m5evt/Firecrest/firmware/display.c

/* 
 * Copyright 2021 m5evt
 * 
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
 */
 
#include <stdlib.h>

#include "firecrest.h"
#include "ssd1306.h"
#include "display.h"



static void drawNumberBig(int bigNum, int offset);
static void drawNumberSmall(int smallNum, int offset, int offsetRow);
static void drawDot(int offset);
static void drawVSWRtoOne(void);

//ICON 45x16
// Per http://www.nongnu.org/avr-libc/user-manual/pgmspace.html
const uint8_t stateIcons[NUMSTATES][ICONWIDTHbits*ICONROWSbytes] PROGMEM = { 
{0x0 , 0x0 , 0x0 , 0x0 , 0x0 , 0x0 , 0x0 , 0x0 , 0x00 , 0x00 , 0x00 , 0x00 , 0x00 , 0x0 , 0x0 , 0x0 , 0x0 , 0x0 , 0x0 , 0x0 , 0x0, 0x0, 0x0 , 0x0 , 0x0, 0x0, 0x0, 0x0, 0x0 , 0x0 , 0x0 , 0x0 , 0x0 , 0x0 , 0x0 , 0x0 , 0x0 , 0x0 , 0x0 , 0x0 , 0x0 , 0x0 , 0x0 , 0x0 , 0x0 , 0x0 , 0x0 , 0x0 , 0x0 , 0x0 , 0x0 , 0x0 , 0x0 , 0x0 , 0x0 , 0x0 , 0x0 , 0x0 , 0x0 , 0x0 , 0x0 , 0x0 , 0x0 , 0x0 , 0x0 , 0x0 , 0x0 , 0x0 , 0x0 , 0x0 , 0x0 , 0x0 , 0x0 , 0x0 , 0x0 , 0x0 , 0x0 , 0x0 , 0x0 , 0x0 , 0x0 , 0x0 , 0x0 , 0x0 , 0x0 , 0x0 , 0x0 , 0x0}, //Freq
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
};

const uint8_t vswrToOne[vswrWIDTHbits * vswrBytes] PROGMEM = {0x0 , 0x0 , 0x0 , 0x0 , 0x0 , 0x0 , 0x0 , 0x3 , 0x3 , 0xff , 0xff , 0x0 , 0x0 , 0x0 , 0x0 , 0x0 , 
0x0 , 0x70 , 0x70 , 0x70 , 0x0 , 0x0 , 0x0 , 0x0 , 0x0 , 0xff , 0xff , 0x0 , 0x0 , 0x0 , 0x0 , 0x0 , 0x0 , 0xe0 , 0xe0 , 0xe0 , 0x0 , 0x0 , 0x0 , 0xc0 , 0xc0 , 0xff , 0xff , 0xc0 , 0xc0 , 0x0 , 0x0 , 0x0};

//Convert Freq to string
void displayFreq(uint32_t freq, uint8_t bat_level) {
	int millions;
	int millions2;
	int hundredthousands;
	int tenthousands;
	int thousands;
  int hundreds;
  int tens;
	
	uint32_t newFreq = freq/4;
	newFreq -= TXOFFSET;

	millions = (int)(newFreq/10000000);
	millions2 = ((newFreq/1000000)%10);
  hundredthousands = ((newFreq/100000)%10);
  tenthousands = ((newFreq/10000)%10);
  thousands = ((newFreq/1000)%10);
  hundreds = ((newFreq/100)%10);
  tens = ((newFreq/10)%10);

	if (millions == 0) {
    drawNumberBig(11,0);
  }
  else {
    drawNumberBig(millions,0);
  }
	drawNumberBig(millions2,BIGNUMbits);
	drawNumberBig(hundredthousands,((BIGNUMbits)*2)+5);
	drawNumberBig(tenthousands,((BIGNUMbits)*3)+5);		  
	drawNumberBig(thousands,((BIGNUMbits)*4)+5);
	drawNumberSmall(hundreds,(((BIGNUMbits)*5)+5), 2);  
	drawNumberSmall(tens,(((BIGNUMbits)*5)+SMALLNUMbits+5), 2);
				
	drawDot(BIGNUMbits*2);

	drawBat(bat_level);
}

void displayFreqSmall(uint32_t rxFreq, uint32_t ritFreq) {
	int millions;
	int millions2;
	int hundredthousands;
	int tenthousands;
	int thousands;
  int hundreds;
  int tens;
  int ones;
	
	rxFreq = rxFreq/4;
	rxFreq -= TXOFFSET;	
	
	millions = (int)(rxFreq/10000000);
	millions2 = ((rxFreq/1000000)%10);
  hundredthousands = ((rxFreq/100000)%10);
  tenthousands = ((rxFreq/10000)%10);
  thousands = ((rxFreq/1000)%10);
  hundreds = ((rxFreq/100)%10);
  tens = ((rxFreq/10)%10);
     
	drawNumberSmall(millions,0,0);
	drawNumberSmall(millions2,SMALLNUMbits, 0);
	drawNumberSmall(hundredthousands,(((SMALLNUMbits)*2)+5),0);  
	drawNumberSmall(tenthousands,(((SMALLNUMbits)*3)+5),0);		
	drawNumberSmall(thousands,(((SMALLNUMbits)*4))+5,0);
	drawNumberSmall(hundreds,(((SMALLNUMbits)*5))+5,0);
	drawNumberSmall(tens,(((SMALLNUMbits)*5)+SMALLNUMbits+5),0);


	ritFreq = ritFreq/4;
	ritFreq -= TXOFFSET;	
    
	if (ritFreq > rxFreq) {
		drawNumberSmall(11,(((SMALLNUMbits)*2)+5),2);  
	}
	else if (ritFreq == rxFreq) {
	  // Do nothing
	}	
	else {
		drawNumberSmall(10,(((SMALLNUMbits)*2)+5),2);  	
	}
		
	ritFreq = abs(ritFreq - rxFreq);
	
  tenthousands = ((ritFreq/10000)%10);
  thousands = ((ritFreq/1000)%10);
  hundreds = ((ritFreq/100)%10);
  tens = ((ritFreq/10)%10);
  ones = ((ritFreq/1)%10);

	drawNumberSmall(thousands,(((SMALLNUMbits)*3)+5),2);		
	drawNumberSmall(hundreds,(((SMALLNUMbits)*4))+5,2);
	drawNumberSmall(tens,(((SMALLNUMbits)*5))+5,2);
	drawNumberSmall(ones,(((SMALLNUMbits)*5)+SMALLNUMbits+5),2);
}

void drawNumberBig(int bigNum, int offset) {
	uint16_t i;
	uint8_t j = 0;
	uint8_t k;

	for (k=1; k<4; k++) {	
		//Fill Icon into main buffer, starting at x,y -> ( (128-45) , 0 )
		for (i=0; i<BIGNUMbits; i++) {
			OLEDbuffer[(i+offset)+(SSD1306_LCDWIDTH*k)] = pgm_read_byte(&(bigNumbers[bigNum][j]));
			j++;
		}
	}	
}

void drawNumberSmall(int smallNum, int offset, int offsetRow) {
	uint16_t i;
	uint8_t j = 0;
	uint8_t k;

	for (k=offsetRow; k<(offsetRow+2); k++) {	
		//Fill Icon into main buffer, starting at x,y -> ( (128-45) , 0 )
		for (i=0; i<SMALLNUMbits; i++) {
			OLEDbuffer[(i+offset)+(SSD1306_LCDWIDTH*k)] = pgm_read_byte(&(smallNumbers[smallNum][j]));
			j++;
		}
	}	
}

void drawDot(int offset) {
	uint16_t i;
	uint8_t j = 0;
	uint8_t k;

	for (k=1; k<4; k++) {	
		//Fill Icon into main buffer, starting at x,y -> ( (128-45) , 0 )
		for (i=0; i<BIGDOTbits; i++) {
			OLEDbuffer[(i+offset)+(SSD1306_LCDWIDTH*k)] = pgm_read_byte(&(bigDot[j]));
			j++;
		}
	}	
}

void drawBat(uint8_t charge) {
	uint16_t i;
	uint8_t j = 0;
	uint8_t k;

	for (k=3; k<4; k++) 	
	{	
		//Fill Icon into main buffer, starting at x,y -> ( (128-45) , 0 )
		for (i=(SSD1306_LCDWIDTH-batWIDTHbits); i<SSD1306_LCDWIDTH; i++) 		
		{
			OLEDbuffer[i+(SSD1306_LCDWIDTH*k)] = pgm_read_byte(&(batIcon[charge][j]));
			j++;
		}
	}	
}

void drawVSWRtoOne(void) {
	uint16_t i;
	uint8_t j = 0;
	uint8_t k;

	for (k=1; k<4; k++) {	
		//Fill Icon into main buffer, starting at x,y -> ( (128-45) , 0 )
		for (i=53; i<(53+vswrWIDTHbits); i++) {
			OLEDbuffer[i+(SSD1306_LCDWIDTH*k)] = pgm_read_byte(&(vswrToOne[j]));
			j++;
		}
	}	
}

void drawMainArea(int item) {
	uint16_t i;
	uint8_t j = 0;
	uint8_t k;

	for (k=1; k<4; k++) {	
		//Fill Icon into main buffer, starting at x,y -> ( (128-45) , 0 )
		for (i=0; i<mainWIDTHbits; i++) {
			OLEDbuffer[i+(SSD1306_LCDWIDTH*k)] = pgm_read_byte(&(mainBigText[item][j]));
			j++;
		}
	}	
}

void drawMainAreaSmall(int item) {
	uint16_t i;
	uint8_t j = 0;
	uint8_t k;

	for (k=1; k<4; k++) {	
		//Fill Icon into main buffer, starting at x,y -> ( (128-45) , 0 )
		for (i=0; i<mainSmallWIDTHbits; i++) {
			OLEDbuffer[i+(SSD1306_LCDWIDTH*k)] = pgm_read_byte(&(mainSmallText[item][j]));
			j++;
		}
	}	
}

void displayChangeStateIcon(uint8_t iconNum) {
	uint16_t i;
	uint8_t j = 0;
	uint8_t k;

	for (k=0; k<2; k++) {				
		//Fill Icon into main buffer, starting at x,y -> ( (128-45) , 0 )
		for (i=(SSD1306_LCDWIDTH-ICONWIDTHbits); i<SSD1306_LCDWIDTH; i++) {
			OLEDbuffer[i+(SSD1306_LCDWIDTH*k)] = pgm_read_byte(&(stateIcons[iconNum][j]));
			j++;
		}
	}
}

void drawIntNumber(uint16_t number) {
	int thousands;
  int hundreds;
  int tens;
  int ones;

  thousands = ((number/1000)%10);
  hundreds = ((number/100)%10);
  tens = ((number/10)%10);
  ones = ((number/1)%10);
    
  if (thousands == 0) {
    drawNumberBig(11, 0);
  }
	else {
    drawNumberBig(thousands,0);
    drawNumberBig(hundreds,BIGNUMbits);
	  drawNumberBig(tens,BIGNUMbits*2);  
	  drawNumberBig(ones,BIGNUMbits*3);
    return;
  }
  if (hundreds == 0) {
    drawNumberBig(11, BIGNUMbits);
  }
  else {
	  drawNumberBig(hundreds,BIGNUMbits);    
	  drawNumberBig(tens,BIGNUMbits*2);  
	  drawNumberBig(ones,BIGNUMbits*3);
    return;	        
  }   
  if (tens == 0) {
    drawNumberBig(11, BIGNUMbits*2);
  }
  else { 
	  drawNumberBig(tens,BIGNUMbits*2);  
	  drawNumberBig(ones,BIGNUMbits*3);	
    return;        
  }    
  drawNumberBig(ones,BIGNUMbits*3);	          
}	

void clearMainArea(void) {
	uint16_t i;
	uint8_t j = 0;
	uint8_t k;

	for (k=0; k<4; k++) {	
    //Fill Icon into main buffer, starting at x,y -> ( (128-45) , 0 )
		for (i=0; i<101; i++) {
			OLEDbuffer[(i)+(SSD1306_LCDWIDTH*k)] = 0;
			j++;
		}
	}	
}

void drawVSWR(uint8_t number) {
  int tens;
  int ones;
	
  tens = ((number/10)%10);
  ones = ((number/1)%10);
   
	drawNumberBig(tens,(BIGNUMbits));
	drawDot(BIGNUMbits*2);	
	drawNumberBig(ones,((BIGNUMbits*2)+5));		
	drawVSWRtoOne();
  ssd1306Refresh();
}
